ViktorNfa/KIBO/CAD/STL files/Battery holder.stl

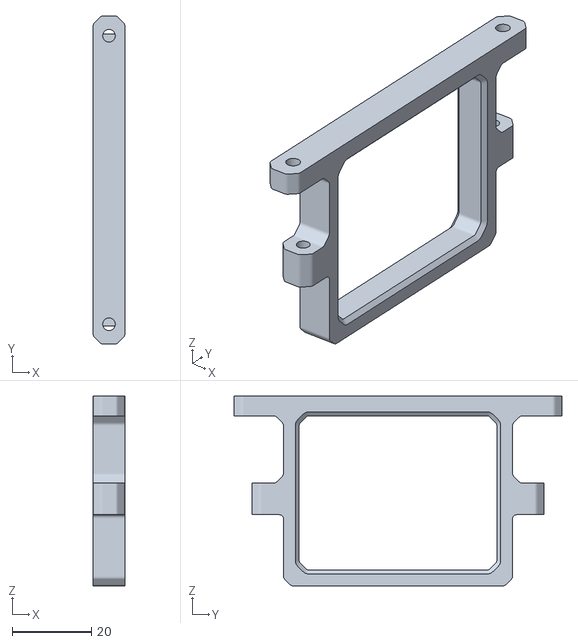
[picture p16: CAD file, 2024-08-09]
CAD/STL files/Battery holder.stl
8.00 x 83.0 x 48.0
