ViktorNfa/KIBO/CAD/STL files/Coxa Left.stl

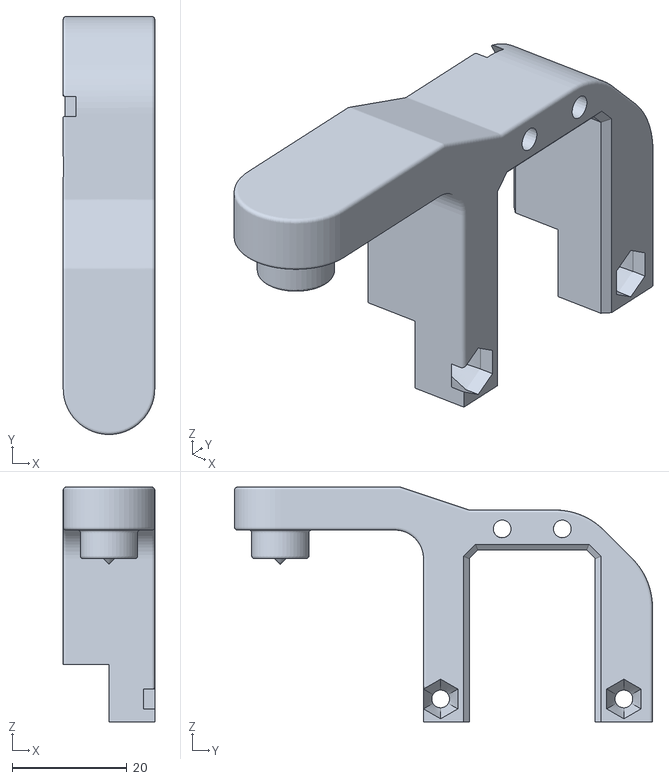
[picture p17: CAD file, 2024-08-03]
CAD/STL files/Coxa Left.stl
16.0 x 73.0 x 41.0
