ViktorNfa/KIBO/CAD/STL files/Servo Back Plate.stl

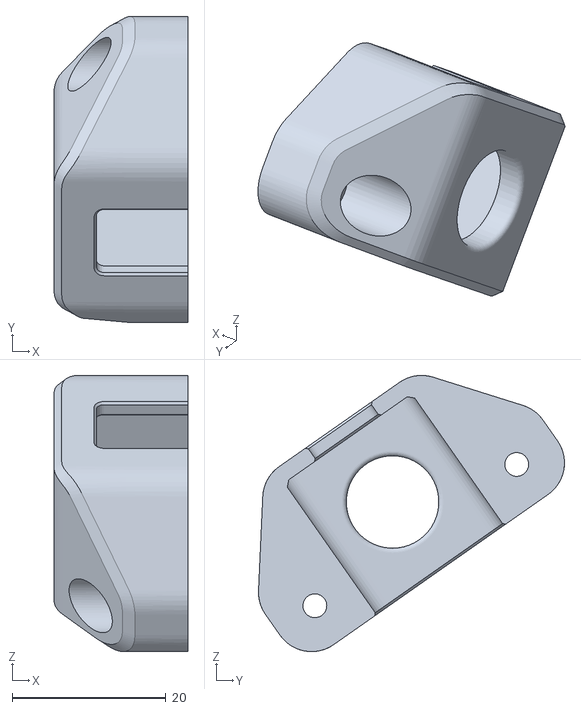
[picture p18: CAD file, 2024-08-03]
CAD/STL files/Servo Back Plate.stl
17.4 x 39.7 x 35.9
