ViktorNfa/KIBO/CAD/STL files/Tibia.stl

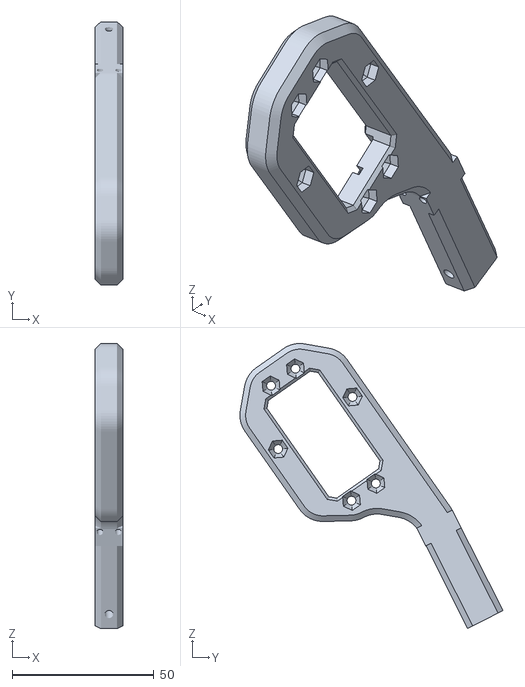
[picture p19: CAD file, 2024-08-03]
CAD/STL files/Tibia.stl
9.80 x 92.7 x 100.4
