ViktorNfa/KIBO/CAD/STL files/Coxa Right.stl

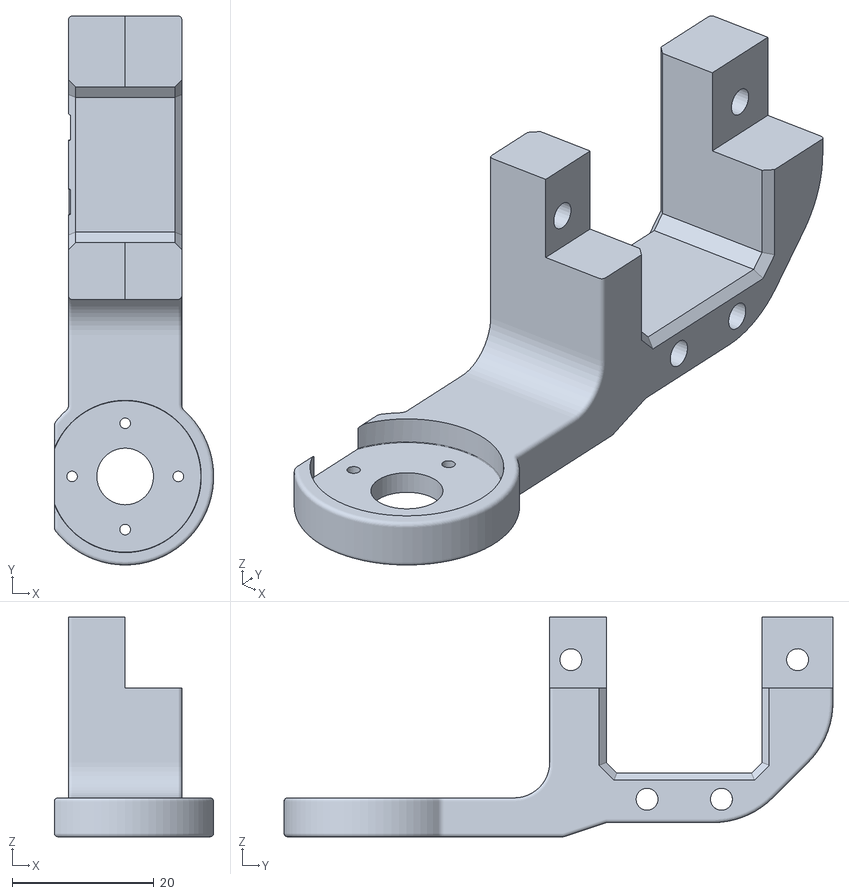
[picture p20: CAD file, 2024-08-03]
CAD/STL files/Coxa Right.stl
22.5 x 77.5 x 31.0
