ViktorNfa/KIBO/CAD/STL files/ring.stl

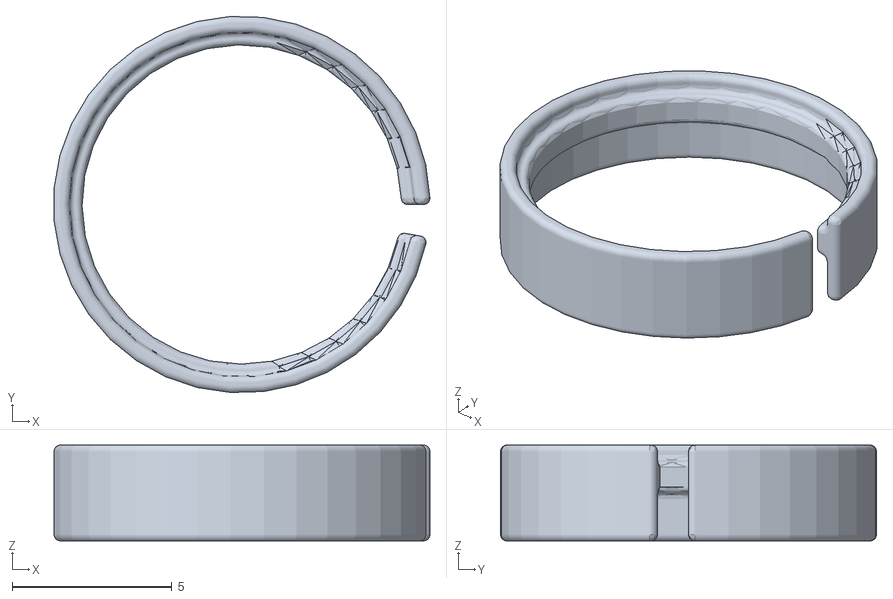
[picture p21: CAD file, 2024-07-19]
CAD/STL files/ring.stl
11.8 x 11.8 x 3.00
