ViktorNfa/KIBO/CAD/STL files/Tibia Slider.stl

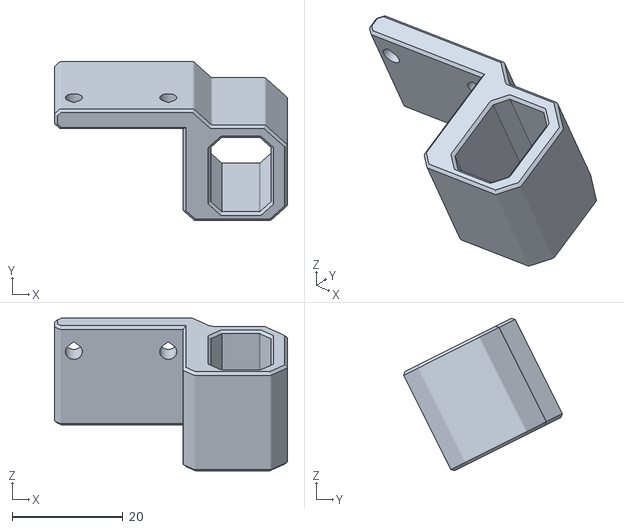
[picture p22: CAD file, 2024-07-19]
CAD/STL files/Tibia Slider.stl
42.0 x 28.6 x 27.5
