ViktorNfa/KIBO/CAD/STL files/Servo Bushing.stl

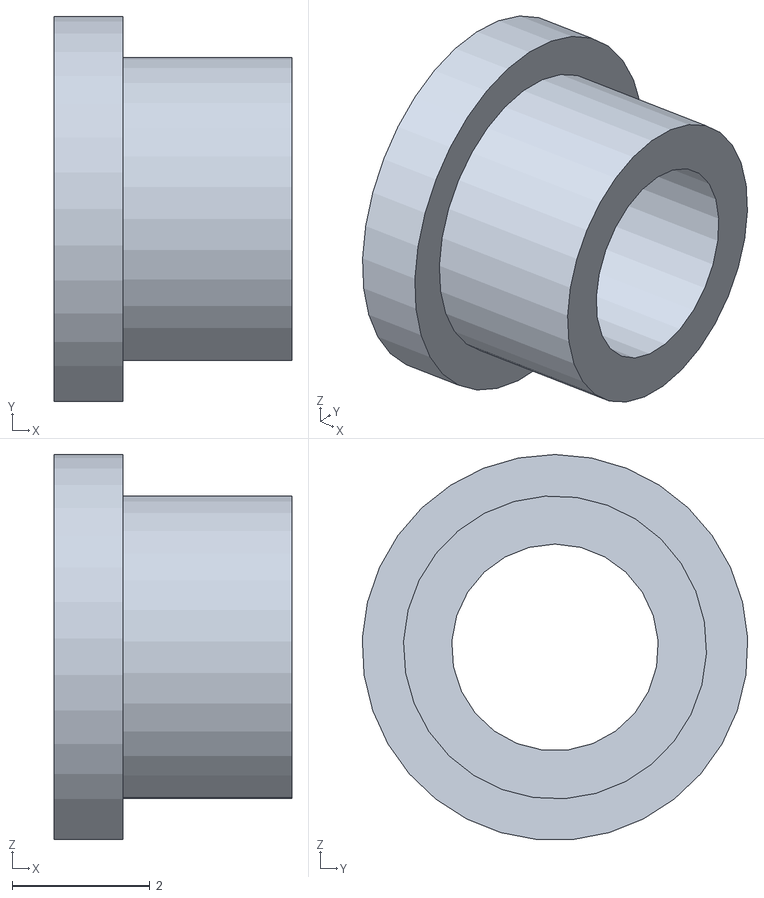
[picture p23: CAD file, 2024-07-19]
CAD/STL files/Servo Bushing.stl
3.45 x 5.59 x 5.59
