ViktorNfa/KIBO/Firmware/esp32_tests/src/main.cpp

#include <Arduino.h>

// Show core temperature to serial monitor
#ifdef __cplusplus
extern "C" {
#endif
uint8_t temprature_sens_read();
#ifdef __cplusplus
}
#endif
uint8_t temprature_sens_read();

uint32_t Freq = 0;

void setup() {
  Serial.begin(115200);

  // Comment or uncomment this to get 10Mhz or 240Mhz CPU frequency
  setCpuFrequencyMhz(240);

  Freq = getCpuFrequencyMhz();
  Serial.print("CPU Freq = ");
  Serial.print(Freq);
  Serial.println(" MHz");
  Freq = getXtalFrequencyMhz();
  Serial.print("XTAL Freq = ");
  Serial.print(Freq);
  Serial.println(" MHz");
  Freq = getApbFrequency();
  Serial.print("APB Freq = ");
  Serial.print(Freq);
  Serial.println(" Hz");
}

void loop() {
  Serial.print("Temperature: ");
  
  // Convert raw temperature in F to Celsius degrees
  Serial.print((temprature_sens_read() - 32) / 1.8);
  Serial.println(" C");
  delay(5000);
}
